jaschlak/JJC/JJC_v2/Fusion/JJCv2_6_upper_body_shell/JJCv2_6_upper_body_shell.stl

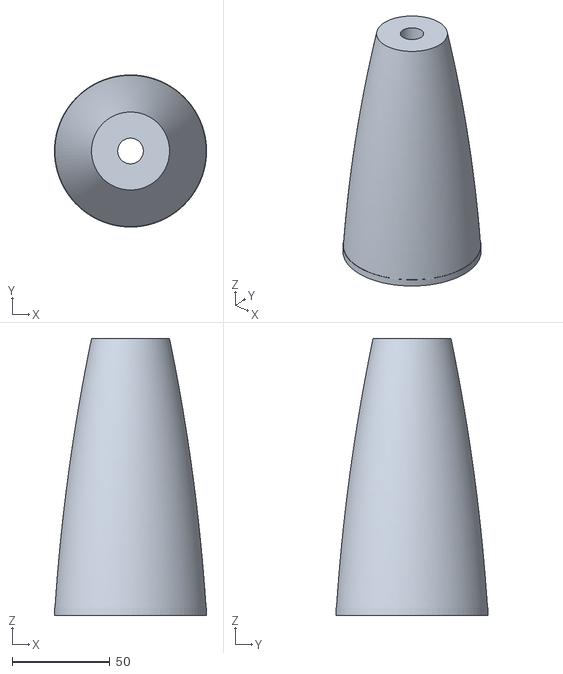
[picture p15: CAD file, 2026-06-10, an earlier design]
JJC_v2/Fusion/JJCv2_6_upper_body_shell/JJCv2_6_upper_body_shell.stl
78.0 x 78.0 x 142.0
