jaschlak/JJC/JJC_v1/Fusion/JJCv1_7_upper_body_shell/JJCv1_7_upper_body_shell.stl

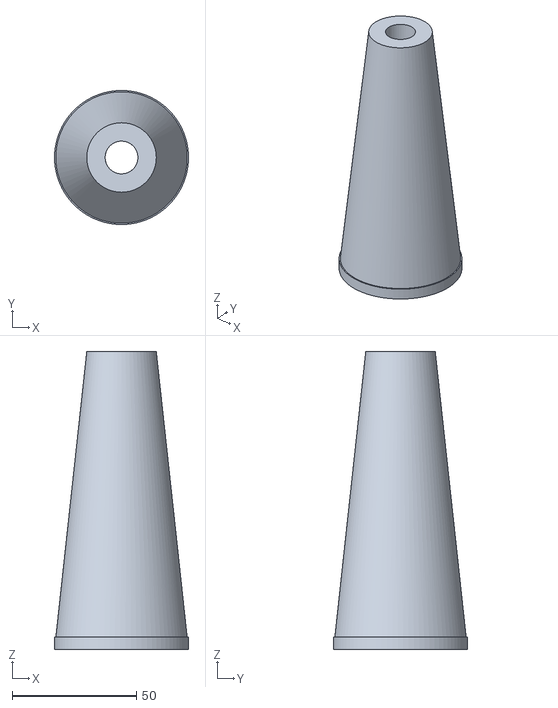
[picture p16: CAD file, 2026-05-31, an earlier design]
JJC_v1/Fusion/JJCv1_7_upper_body_shell/JJCv1_7_upper_body_shell.stl
54.0 x 54.0 x 120.0
